OLIMEX/ESP32-S3-DevKit-LiPo/SOFTWARE/Arduino/Motion-detection-ESP32-S3/4.jpg

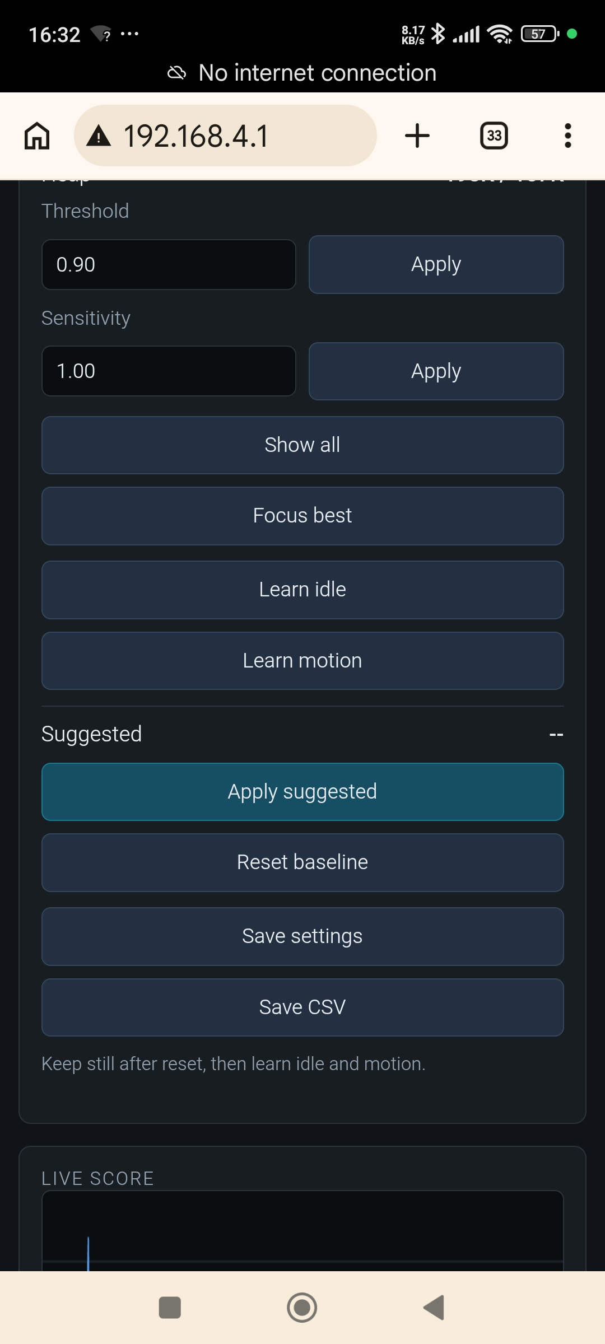
SOFTWARE/Arduino/Motion-detection-ESP32-S3/4.jpg
